TweetyDaBird/Little-Big-Scroll/Images/IMG_0173.JPEG

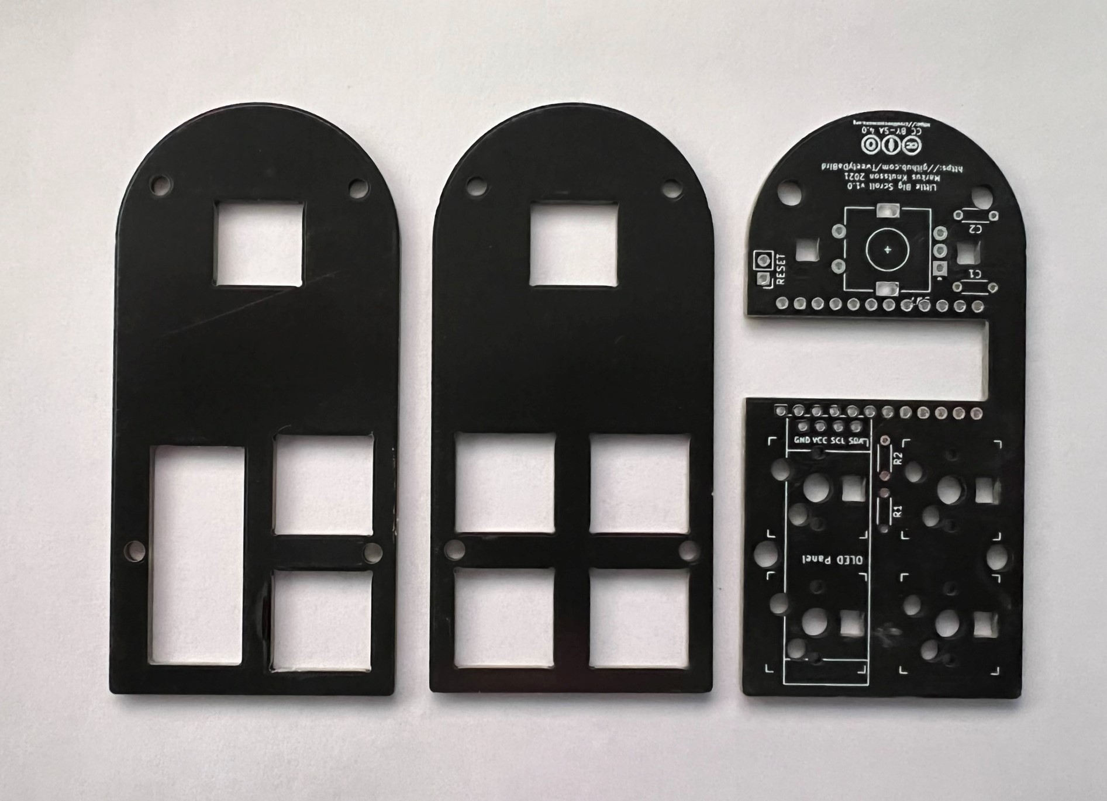
Images/IMG_0173.JPEG
