TweetyDaBird/Little-Big-Scroll/Images/IMG_0174.JPEG

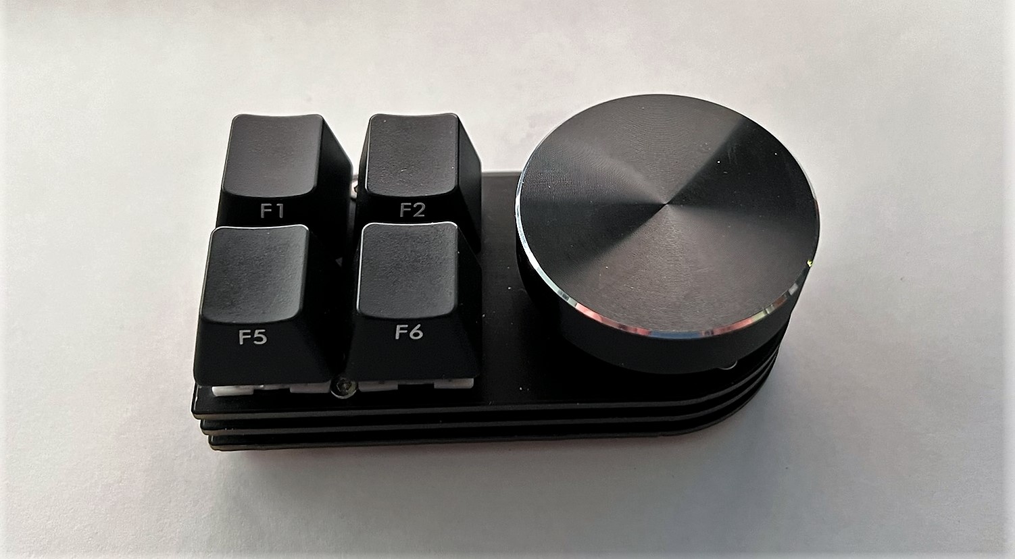
Images/IMG_0174.JPEG
