TweetyDaBird/Little-Big-Scroll/Images/IMG_0198.jpeg

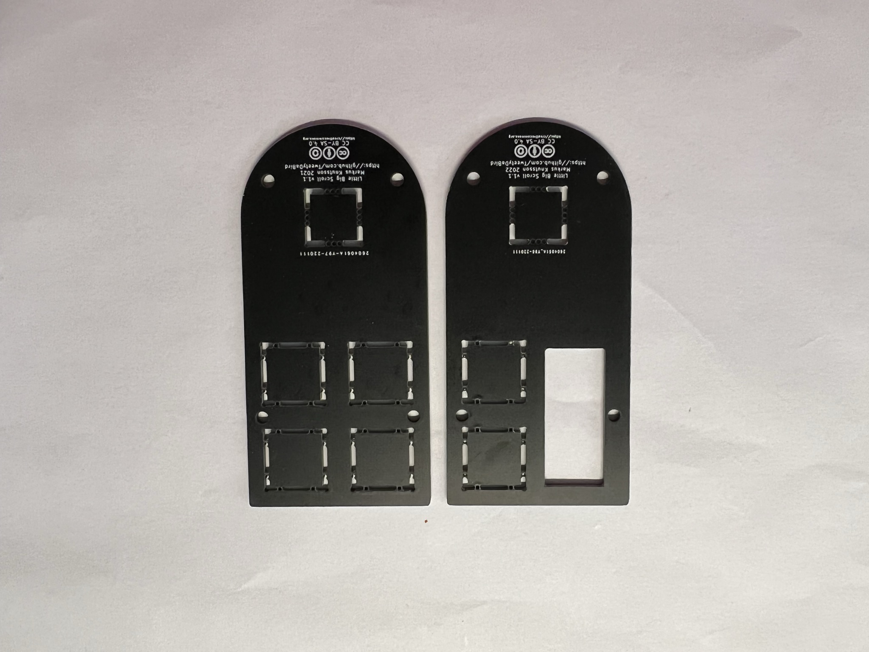
Images/IMG_0198.jpeg
