TweetyDaBird/Little-Big-Scroll/Images/IMG_0426.JPEG

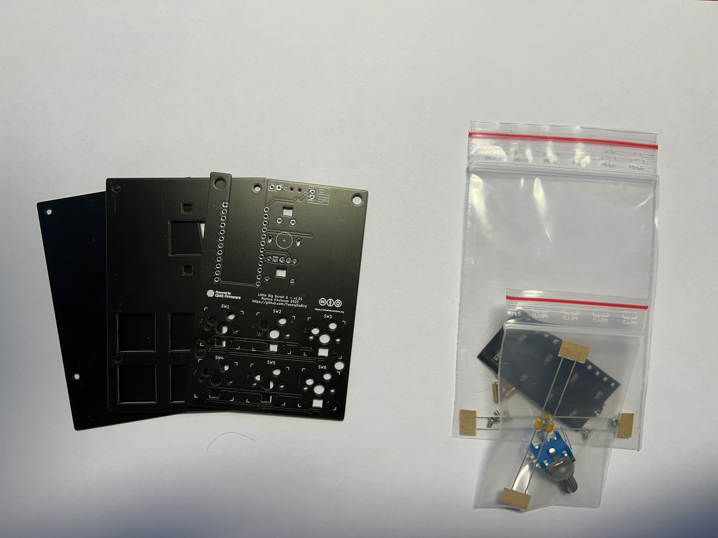
Images/IMG_0426.JPEG
