TweetyDaBird/Little-Big-Scroll/Images/IMG_0426_2.jpeg

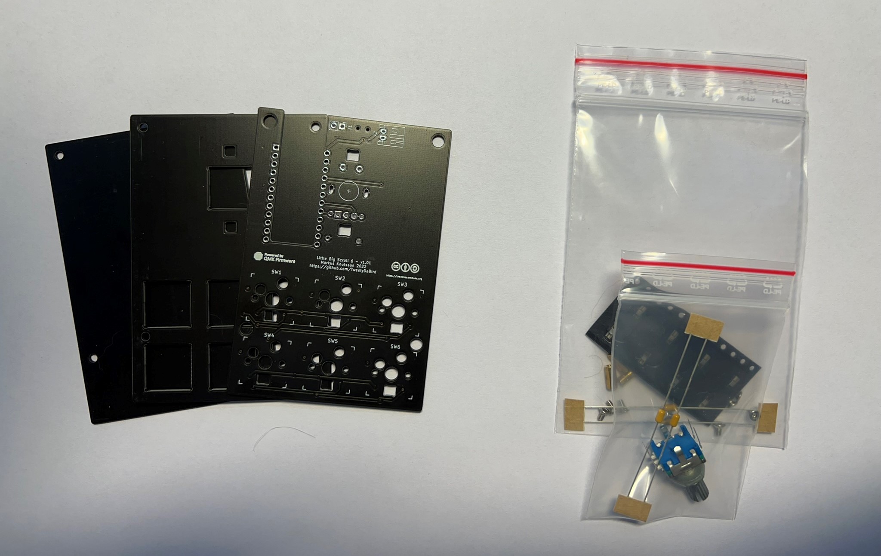
Images/IMG_0426_2.jpeg
