TweetyDaBird/Little-Big-Scroll/Images/IMG_0427.JPEG

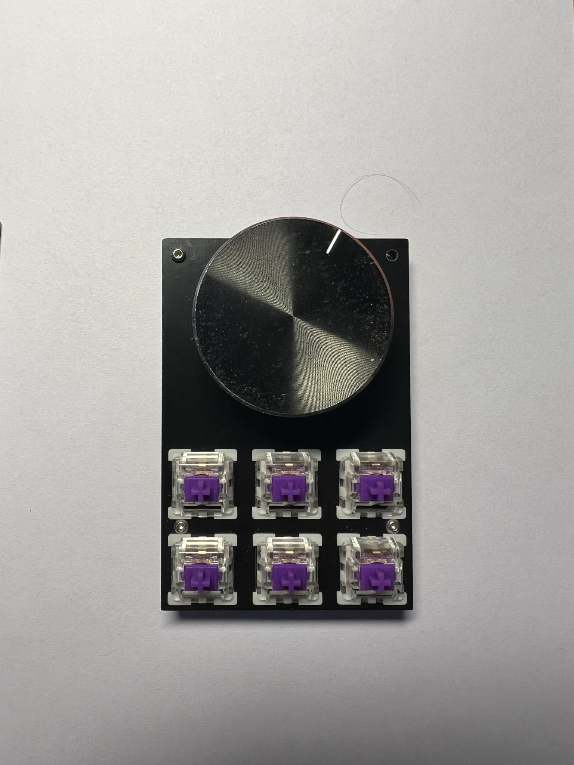
Images/IMG_0427.JPEG
