TweetyDaBird/Little-Big-Scroll/Images/IMG_0428.JPEG

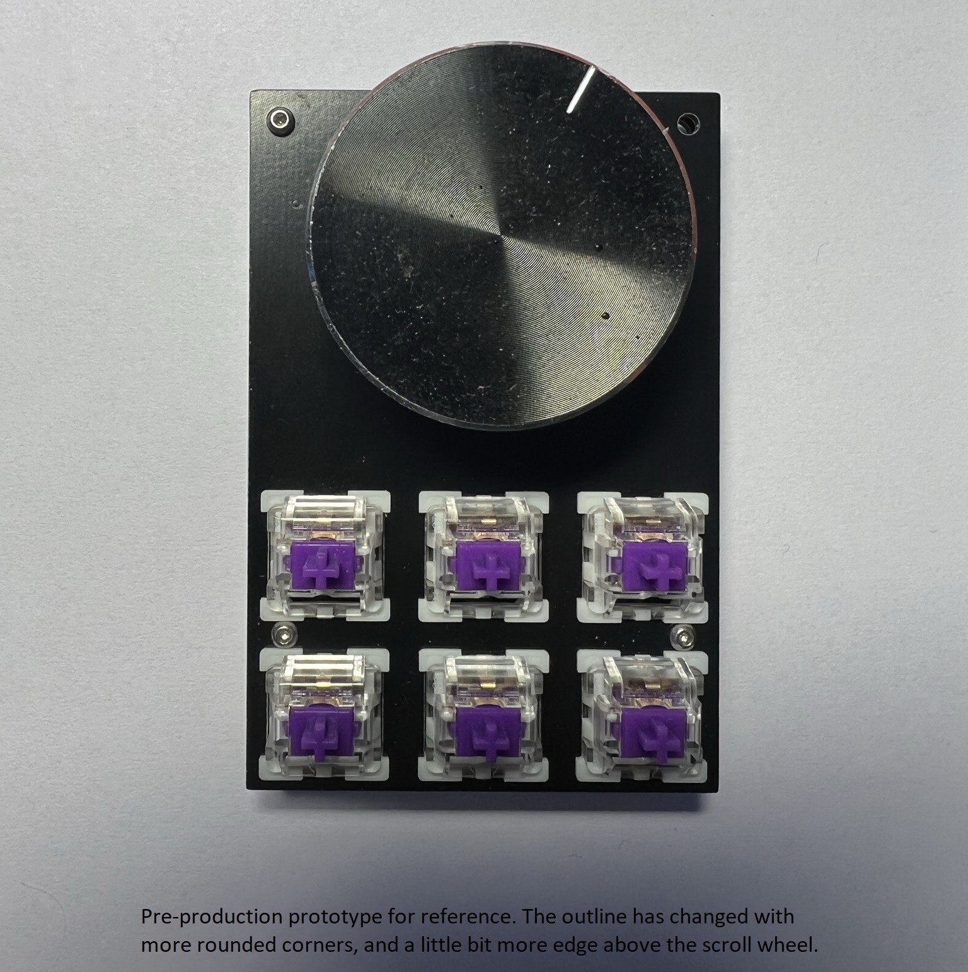
Images/IMG_0428.JPEG
