TweetyDaBird/Little-Big-Scroll/Images/Little Big Scroll 6 .jpg

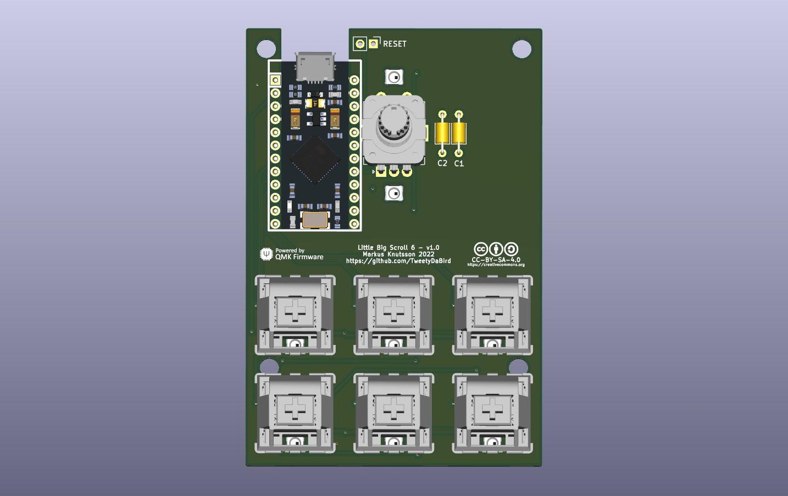
Images/Little Big Scroll 6 .jpg
