TweetyDaBird/Little-Big-Scroll/Images/Little_Big_Scroll_4_back2.jpg

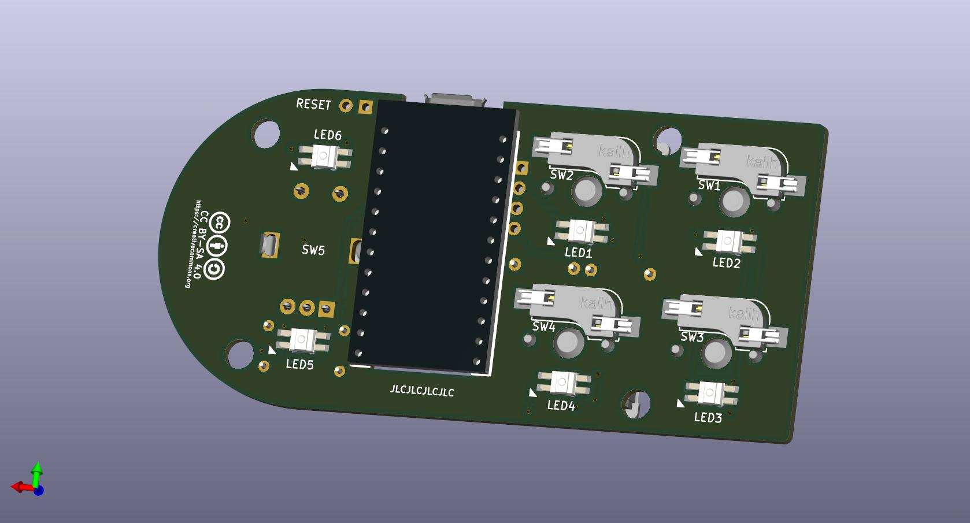
Images/Little_Big_Scroll_4_back2.jpg
